aharris236/GeeetechSKRMod/Notes/Centre_Bar_Cable_Gap.jpg

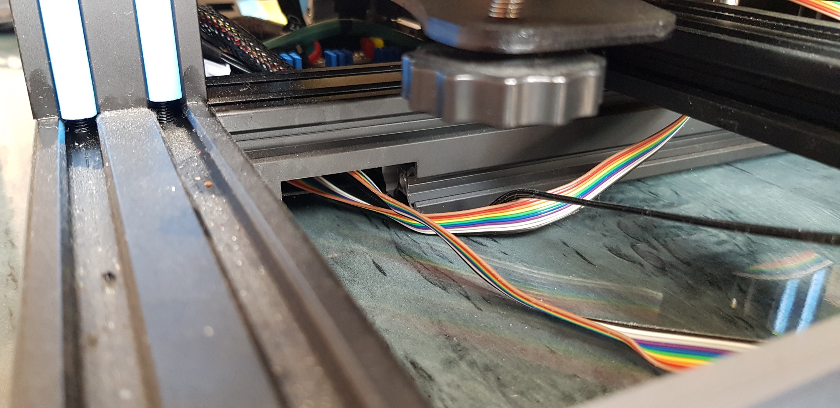
Notes/Centre_Bar_Cable_Gap.jpg
