aharris236/GeeetechSKRMod/Notes/Crossbar.jpg

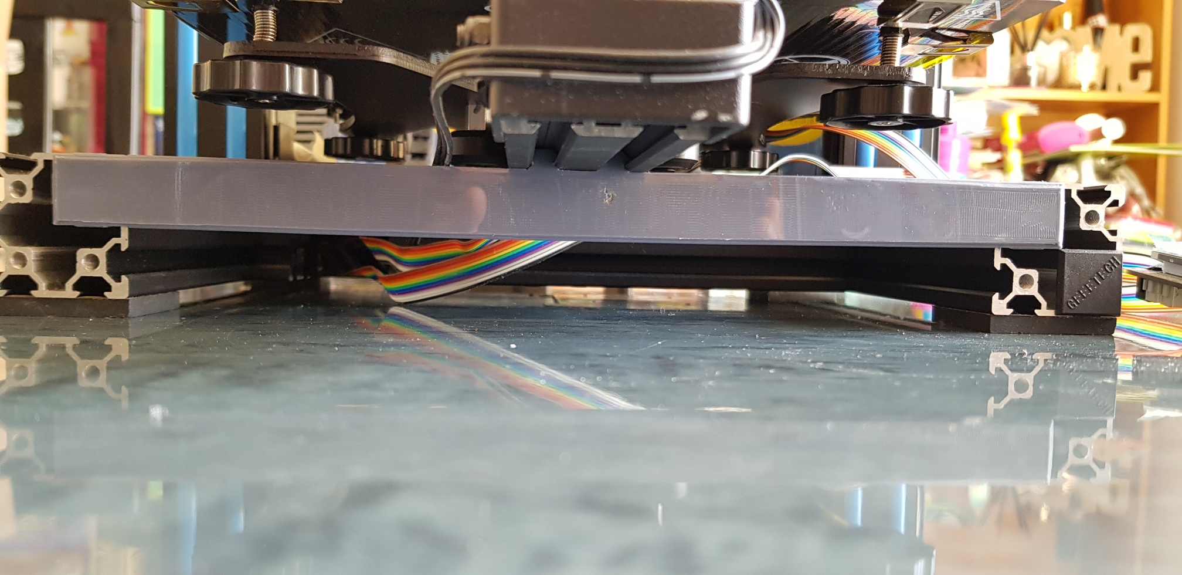
Notes/Crossbar.jpg
