aharris236/GeeetechSKRMod/Notes/Original_Mainboard_and_Controller.jpg

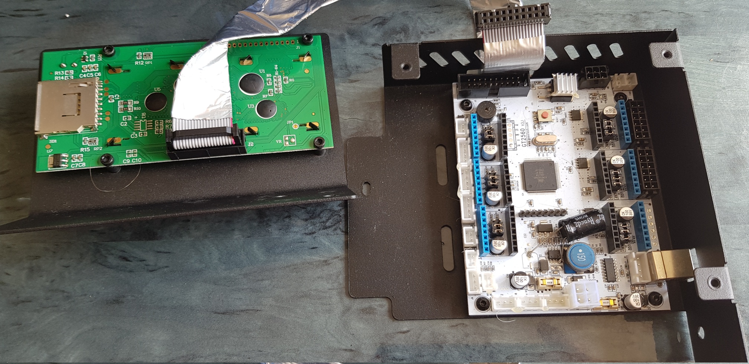
Notes/Original_Mainboard_and_Controller.jpg
