aharris236/GeeetechSKRMod/Notes/Part_Cooler_3D_Touch.jpg

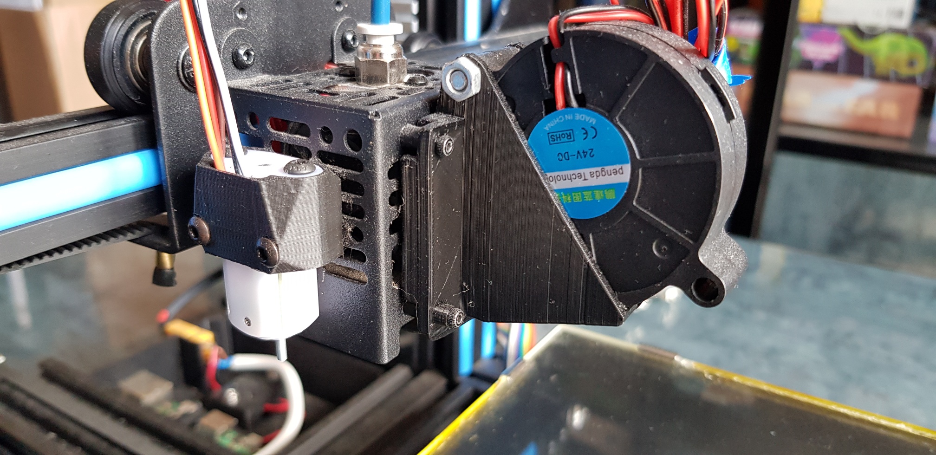
Notes/Part_Cooler_3D_Touch.jpg
