aharris236/GeeetechSKRMod/Notes/Raspberry_Pi_DCDC.jpg

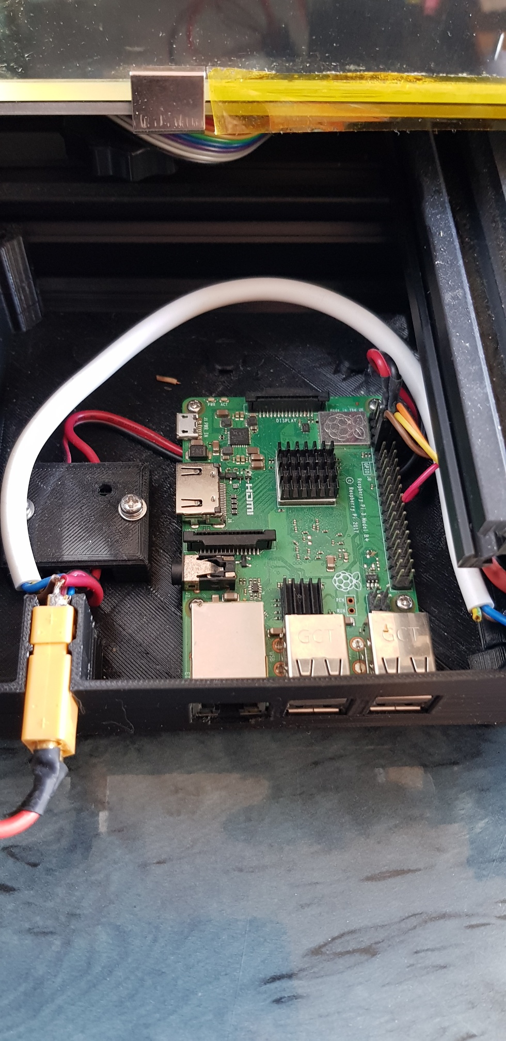
Notes/Raspberry_Pi_DCDC.jpg
