aharris236/GeeetechSKRMod/Notes/Rear_Box_Cable_Nightmare.jpg

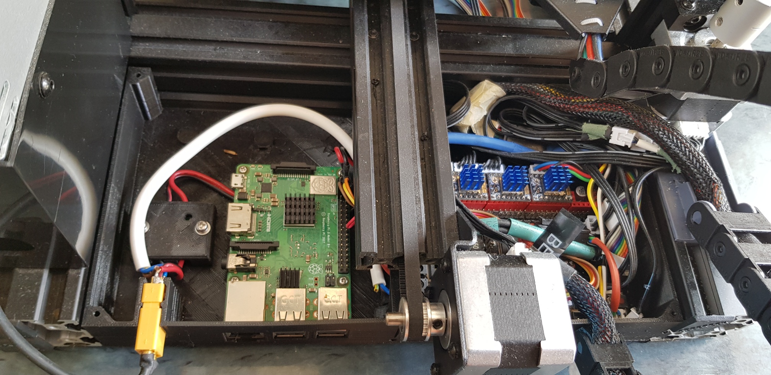
Notes/Rear_Box_Cable_Nightmare.jpg
