aharris236/GeeetechSKRMod/Notes/Z_Axis_Chain_Lower_Mount.jpg

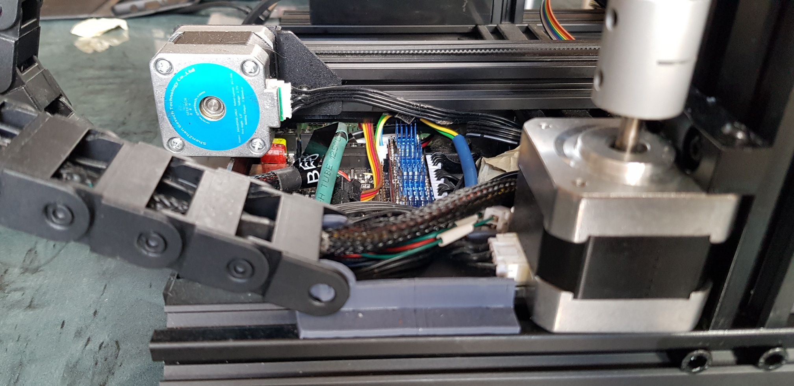
Notes/Z_Axis_Chain_Lower_Mount.jpg
