aharris236/GeeetechSKRMod/Notes/Z_Axis_Upper_Mount.jpg

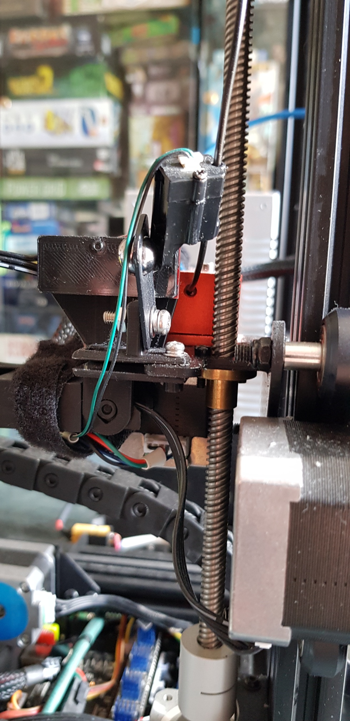
Notes/Z_Axis_Upper_Mount.jpg
