aharris236/GeeetechSKRMod/Notes/Z_Max.jpg

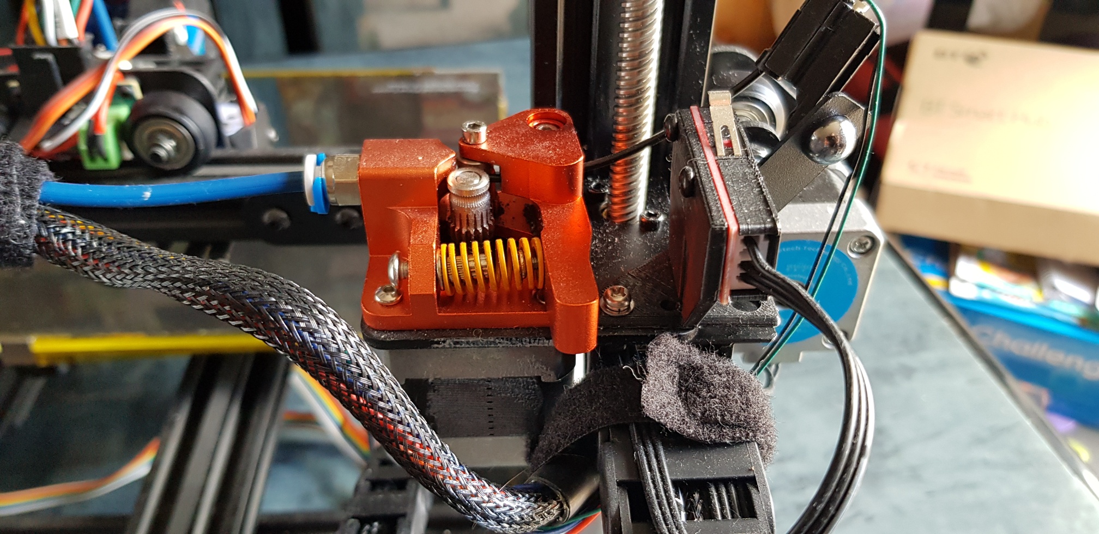
Notes/Z_Max.jpg
